SakuGlumoff/iida_devkit/hardware/img/sara-r5-sysintegrmanual-ant.png

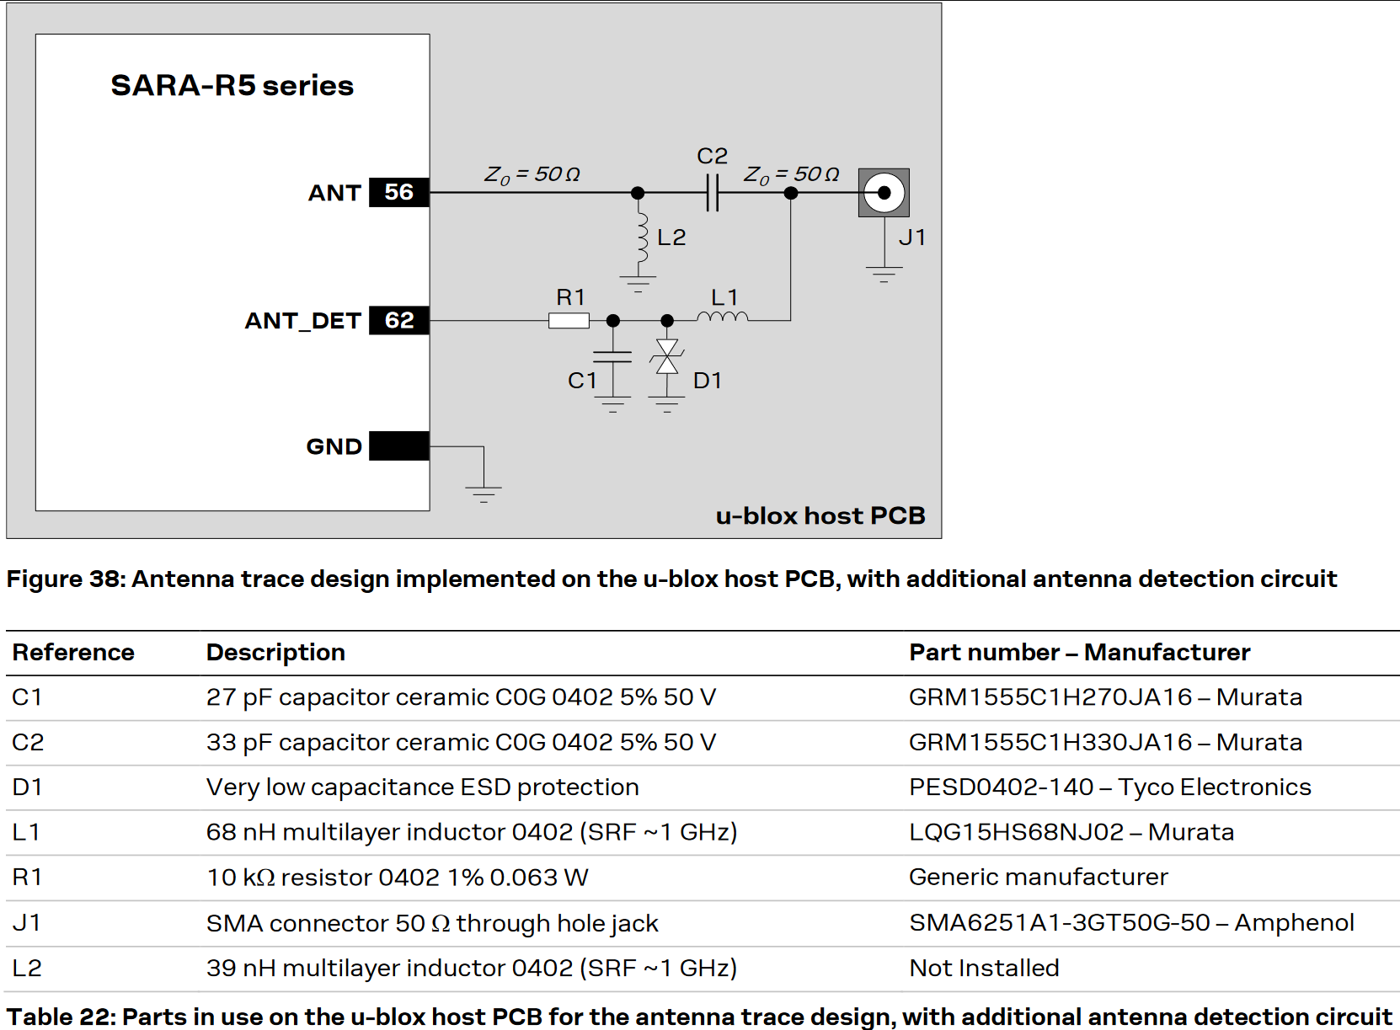
hardware/img/sara-r5-sysintegrmanual-ant.png
