SakuGlumoff/iida_devkit/hardware/img/sara-r5-sysintegrmanual-sim.png

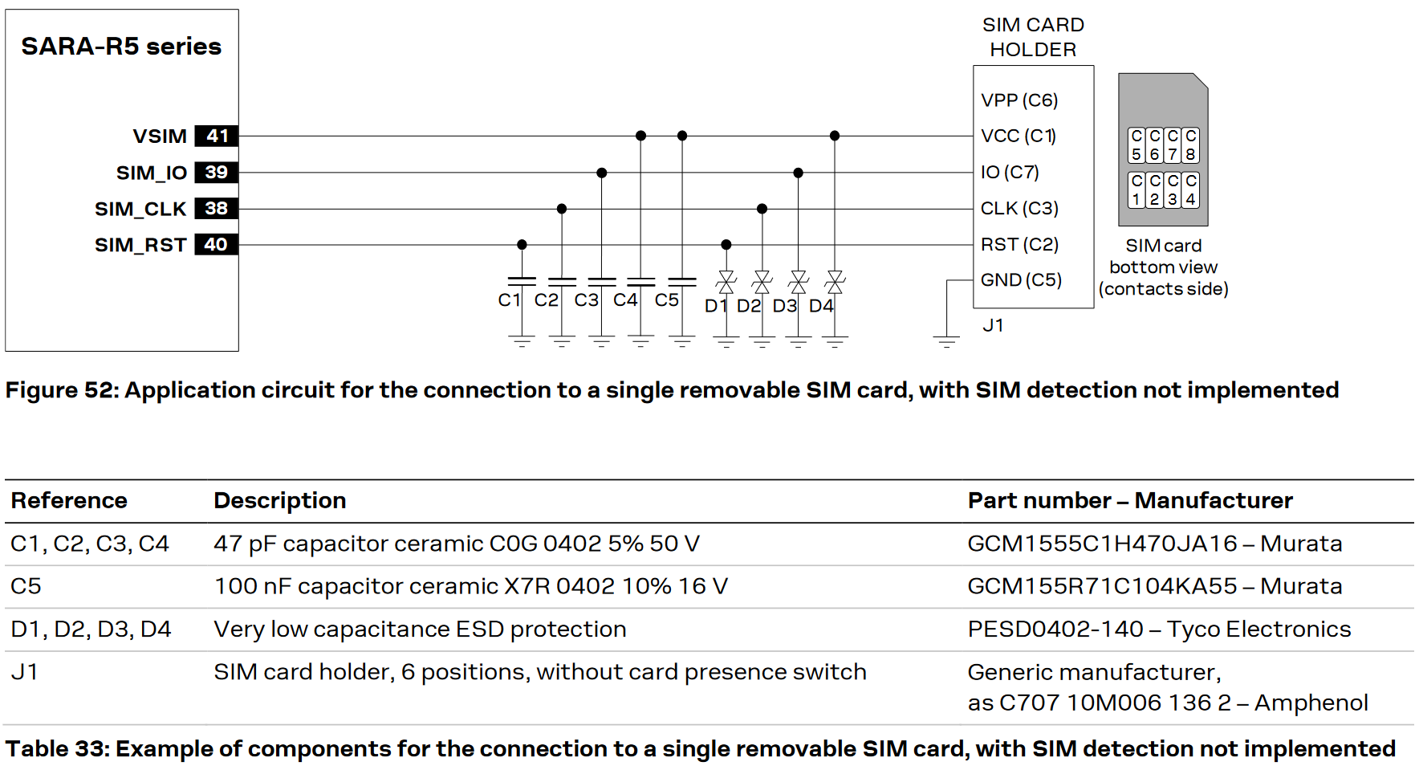
hardware/img/sara-r5-sysintegrmanual-sim.png
