SakuGlumoff/iida_devkit/firmware/include/pinmap.hpp

#pragma once

#define LED_DBG_A_Port GPIOA
#define LED_DBG_A_Pin  10
#define LED_DBG_A      LED_DBG_A_Port, LED_DBG_A_Pin

#define LED_DBG_B_Port GPIOA
#define LED_DBG_B_Pin  9
#define LED_DBG_B      LED_DBG_B_Port, LED_DBG_B_Pin

#define LED_DBG_C_Port GPIOA
#define LED_DBG_C_Pin  8
#define LED_DBG_C      LED_DBG_C_Port, LED_DBG_C_Pin

#define LED_DBG_D_Port GPIOB
#define LED_DBG_D_Pin  15
#define LED_DBG_D      LED_DBG_D_Port, LED_DBG_D_Pin

#define DBG_UART_TX_Port GPIOA
#define DBG_UART_TX_Pin  2
#define DBG_UART_TX      DBG_UART_TX_Port, DBG_UART_TX_Pin

#define DBG_UART_RX_Port GPIOA
#define DBG_UART_RX_Pin  3
#define DBG_UART_RX      DBG_UART_RX_Port, DBG_UART_RX_Pin
