SakuGlumoff/iida_devkit/firmware/include/etl_profile.h

#ifndef __ETL_PROFILE_H__
#define __ETL_PROFILE_H__

#define ETL_VERBOSE_ERRORS
#define ETL_CHECK_PUSH_POP
#define ETL_ISTRING_REPAIR_ENABLE
#define ETL_IVECTOR_REPAIR_ENABLE
#define ETL_IDEQUE_REPAIR_ENABLE
#define ETL_NO_STL
#define ETL_IN_UNIT_TEST

#endif
